stahlnow/mixerli/enclosure/v1.0/case/top_cutout.dxf

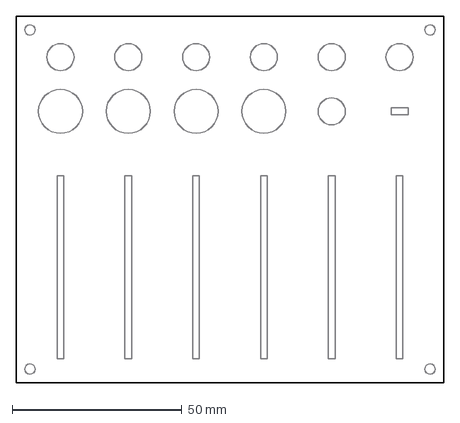
[picture p16: CAD file, 2018-02-25, an earlier design]
enclosure/v1.0/case/top_cutout.dxf
126.0 x 108.0 mm
