stahlnow/mixerli/enclosure/v1.0/case/back_cutout.dxf

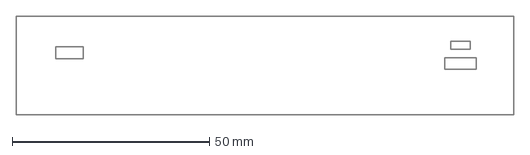
[picture p17: CAD file, 2018-02-25, an earlier design]
enclosure/v1.0/case/back_cutout.dxf
126.0 x 25.0 mm
