stahlnow/mixerli/enclosure/v1.0/Turn knob.STEP

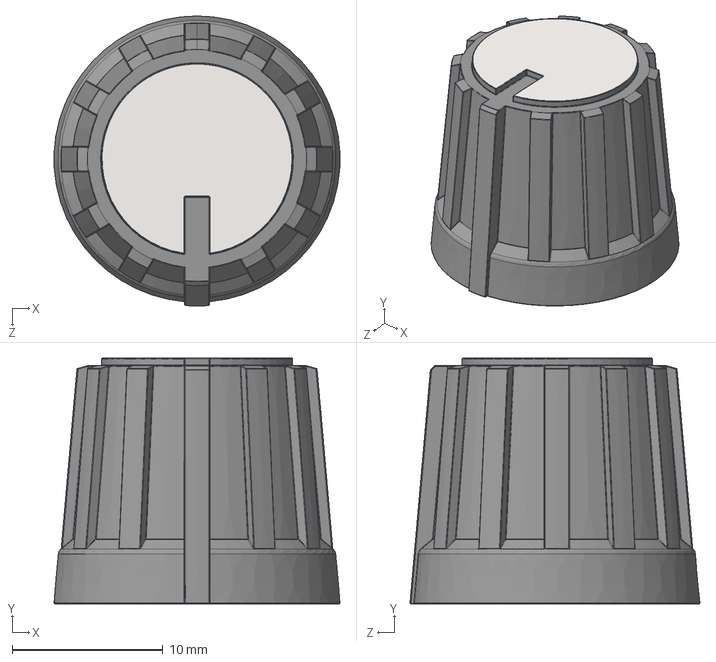
[picture p18: CAD file, 2018-02-25, an earlier design]
enclosure/v1.0/Turn knob.STEP
19.0 x 16.3 x 19.2 mm
