stahlnow/mixerli/enclosure/v1.0/1050170001.stp

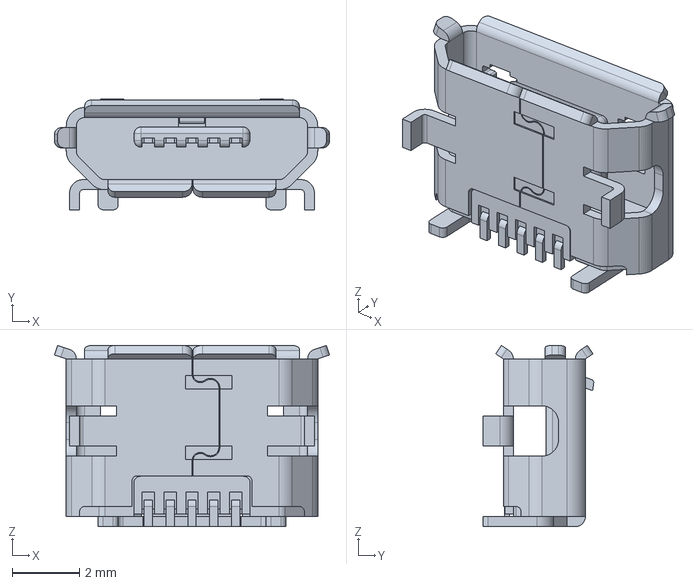
[picture p19: CAD file, 2018-02-25, an earlier design]
enclosure/v1.0/1050170001.stp
8.20 x 3.30 x 5.40 mm
